ThomasBuzer/Serre_connectee/Arduino/final_version/images.cpp

#include "fonctions.h"
#include "esp_camera.h"
#include "Base64.h"
#include <WiFiClientSecure.h>


#define PWDN_GPIO_NUM     32
#define RESET_GPIO_NUM    -1
#define XCLK_GPIO_NUM      0
#define SIOD_GPIO_NUM     26
#define SIOC_GPIO_NUM     27

#define Y9_GPIO_NUM       35
#define Y8_GPIO_NUM       34
#define Y7_GPIO_NUM       39
#define Y6_GPIO_NUM       36
#define Y5_GPIO_NUM       21
#define Y4_GPIO_NUM       19
#define Y3_GPIO_NUM       18
#define Y2_GPIO_NUM        5
#define VSYNC_GPIO_NUM    25
#define HREF_GPIO_NUM     23
#define PCLK_GPIO_NUM     22



const char* myDomain =  "script.google.com";
String mimeType = "&mimetype=image/jpeg";
String myImage = "&data=";
String imagePost = "&image=1";
String myFilename = "filename=ESP32-CAM.jpg";

int waitingTime = 30000; //Wait 30 seconds to google response.


void setupCam(){

  camera_config_t config;
  config.ledc_channel = LEDC_CHANNEL_0;
  config.ledc_timer = LEDC_TIMER_0;
  config.pin_d0 = Y2_GPIO_NUM;
  config.pin_d1 = Y3_GPIO_NUM;
  config.pin_d2 = Y4_GPIO_NUM;
  config.pin_d3 = Y5_GPIO_NUM;
  config.pin_d4 = Y6_GPIO_NUM;
  config.pin_d5 = Y7_GPIO_NUM;
  config.pin_d6 = Y8_GPIO_NUM;
  config.pin_d7 = Y9_GPIO_NUM;
  config.pin_xclk = XCLK_GPIO_NUM;
  config.pin_pclk = PCLK_GPIO_NUM;
  config.pin_vsync = VSYNC_GPIO_NUM;
  config.pin_href = HREF_GPIO_NUM;
  config.pin_sscb_sda = SIOD_GPIO_NUM;
  config.pin_sscb_scl = SIOC_GPIO_NUM;
  config.pin_pwdn = PWDN_GPIO_NUM;
  config.pin_reset = RESET_GPIO_NUM;
  config.xclk_freq_hz = 20000000;
  config.pixel_format = PIXFORMAT_JPEG;
  config.frame_size = FRAMESIZE_SVGA;  // UXGA|SXGA|XGA|SVGA|VGA|CIF|QVGA|HQVGA|QQVGA
  config.jpeg_quality = 10;
  config.fb_count = 1;

  esp_err_t err = esp_camera_init(&config);
  if (err != ESP_OK) {
    Serial.printf("Camera init failed with error 0x%x", err);
    delay(1000);
    ESP.restart();
  }
}


void saveCapturedImage() {
  
  String myScript = "/macros/s/" + GOOGLE_SCRIPT_ID + "/exec";
  
  Serial.println("Connect to " + String(myDomain));
  WiFiClientSecure client;
  client.setInsecure();
  String address = myDomain+myScript;
  if (client.connect(myDomain, 443)) {
    Serial.println("Connection successful");

    //allumage de la LED pour la photo
    digitalWrite(whiteLed, LED_PHOTO);
    delay(10);
    camera_fb_t * fb = NULL;
    fb = esp_camera_fb_get();  
    if(!fb) {
      Serial.println("Camera capture failed");
      delay(1000);
      ESP.restart();
      return;
    }
    //Extinction de la LED
    digitalWrite(whiteLed, LOW);
    
  
    char *input = (char *)fb->buf;
    char output[base64_enc_len(3)];
    String imageFile = "";
    for (int i=0;i<fb->len;i++) {
      base64_encode(output, (input++), 3);
      if (i%3==0) imageFile += urlencode(String(output));
    }
    String Data = myFilename+imagePost+mimeType+myImage;
    
    esp_camera_fb_return(fb);
    
    Serial.println("Send a captured image to Google Drive.");
    
    client.println("POST " + myScript + " HTTP/1.1");
    client.println("Host: " + String(myDomain));
    client.println("Content-Length: " + String(Data.length()+imageFile.length()));
    client.println("Content-Type: application/x-www-form-urlencoded");
    client.println();
    
    client.print(Data);
    int Index;
    for (Index = 0; Index < imageFile.length(); Index = Index+1000) {
      client.print(imageFile.substring(Index, Index+1000));
    }
    
    Serial.println("Waiting for response.");
    long int StartTime=millis();
    while (!client.available()) {
      Serial.print(".");
      delay(100);
      if ((StartTime+waitingTime) < millis()) {
        Serial.println();
        Serial.println("No response.");
        //If you have no response, maybe need a greater value of waitingTime
        break;
      }
    }
    Serial.println();   
    while (client.available()) {
      Serial.print(char(client.read()));
    }  
  } else {         
    Serial.println("Connected to " + String(myDomain) + " failed.");
  }
  client.stop();
}

String urlencode(String str)
{
    String encodedString="";
    char c;
    char code0;
    char code1;
    char code2;
    for (int i =0; i < str.length(); i++){
      c=str.charAt(i);
      if (c == ' '){
        encodedString+= '+';
      } else if (isalnum(c)){
        encodedString+=c;
      } else{
        code1=(c & 0xf)+'0';
        if ((c & 0xf) >9){
            code1=(c & 0xf) - 10 + 'A';
        }
        c=(c>>4)&0xf;
        code0=c+'0';
        if (c > 9){
            code0=c - 10 + 'A';
        }
        code2='\0';
        encodedString+='%';
        encodedString+=code0;
        encodedString+=code1;
        //encodedString+=code2;
      }
      yield();
    }
    return encodedString;
}
